djtersteegc/smartportsd/docs/combined-boards.jpg

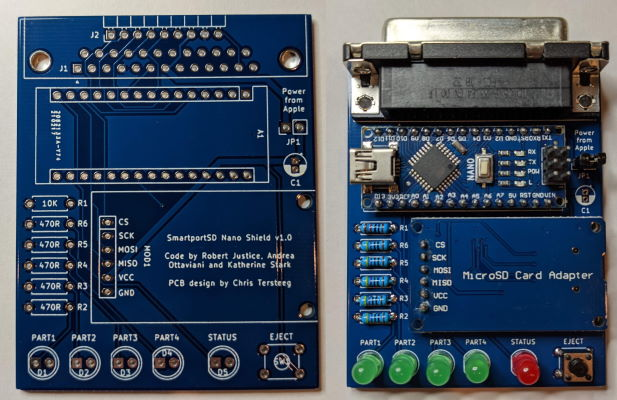
docs/combined-boards.jpg
