djtersteegc/smartportsd/docs/DB1-0mm-Male-Pin-for-DB-Terminal-Connector-Gold-plated-for-Nixie-Clock-Tubes-IN12-IN18.jpg_.webp

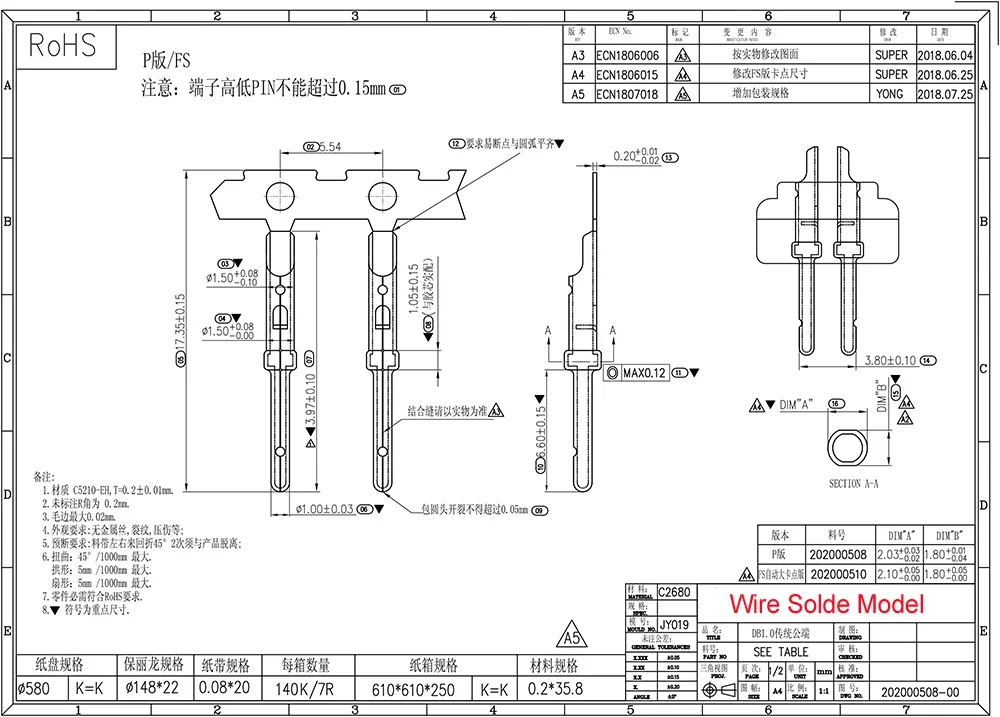
docs/DB1-0mm-Male-Pin-for-DB-Terminal-Connector-Gold-plated-for-Nixie-Clock-Tubes-IN12-IN18.jpg_.webp
