djtersteegc/smartportsd/docs/enclosure.jpg

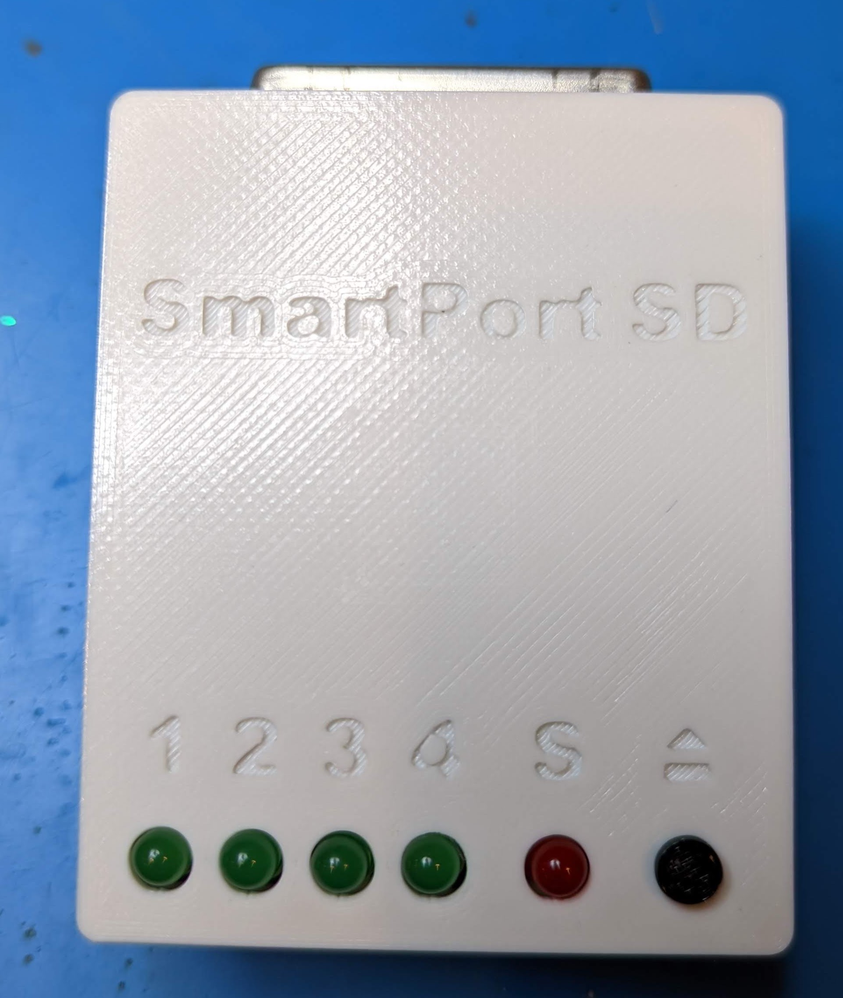
docs/enclosure.jpg
