djtersteegc/smartportsd/docs/social.jpg

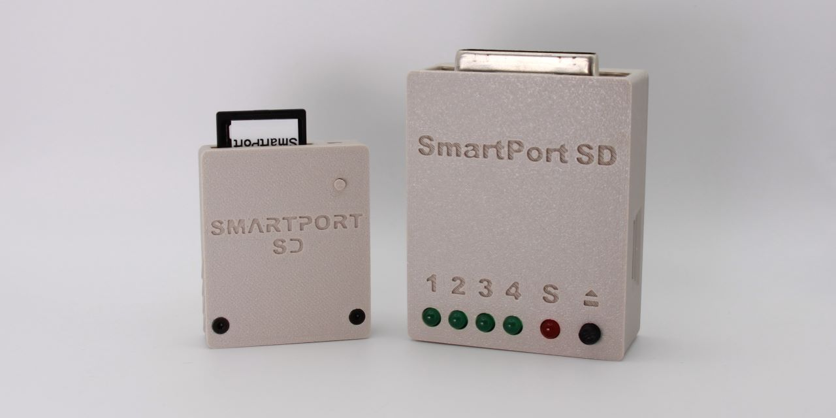
docs/social.jpg
